hak8or/WeatherSpot/firmware/Network.cpp

#include <SoftwareSerial.h>
#include "Arduino.h"
#include "Heartbeat.h"
#include "Network.h"
#include "Sensors.h"

/**
 * @brief Sends a peice of data over TCP to our backend.
 * @details Does a DNS lookup for our backend, sets up a TCP connection, and sends our data.
 *
 * @param  sensor_data The sensor data struct worth of data we will be sending.
 * @param  series      What series (location) we want our data to be sent to.
 * 
 * @return             True if data was sent succesfully, false if otherwise.
 */
bool Network::send_packet(const Sensors::Sensor_data sensor_data, const String series){
	// Connect to our server.
	if (send_command("AT+CIPSTART=\"TCP\",\"104.131.85.242\",80", "OK", 2, 1500))
		Serial.println(F("Wifi TCP connection created."));
	else{
		Serial.println(F("Wifi TCP connection creation failed."));
		return false;
	}

	// Construct our POST request.
	String post_request = "POST /db/query.php?";
	post_request = post_request + "series=" + series;
	post_request = post_request + "&temperature=" + String(sensor_data.temperature_f);
	post_request = post_request + "&humidity=" + String(sensor_data.humidity);
	post_request = post_request + "&pressure=" + String(sensor_data.pressure);
	post_request = post_request + "&lighting=" + String(sensor_data.light);
	post_request = post_request + "\r\n";

	// Construct the command to begin our POST request.
	String command = "AT+CIPSEND=" + String(post_request.length());

	Serial.print(F("Sending:\n\t"));
	Serial.println(command);
	Serial.print(F("With the contents:\n\t"));
	Serial.println(post_request);

	// Tell the wifi module we want to send a HTTP request.
	if (send_command(command, ">", 1, 1500))
		Serial.println(F("Wifi queried for HTTP contents."));
	else{
		Serial.println(F("Wifi module didn't query what http contents to send, error."));
		return false;
	}

	// And now we send our POST request.
	if (send_command(post_request, "OK", 2, 5000))
		Serial.println(F("Wifi POST request sent succesfully."));
	else{
		Serial.println(F("Wifi POST request failed."));
		return false;
	}

	// It seems that CIPSEND automatically closes the TCP connection or our backend
	// terminates the TCP connection, so CIPCLOSE isn't needed.
	return true;
}

/**
 * @brief Connects to a wireless network using the ESP module.
 * 
 * @param SSID      The SSID of the wireless network we want to connect to.
 * @param password  The password of the wireless network we want to connect to.
 * 
 * @return True if we were able to connect to the network and get an IP, false if otherwise.
 */
bool Network::init_wireless(const String SSID, const String password){
	// Generate the member object
	// Pin D3 -> RX
	// Pin D4 -> TX
	wifi_serial = new SoftwareSerial(4,3);
	wifi_serial->begin(9600);

	// Rest the module so it is in a known state and check if it works.
	if (send_command("AT+RST", "OK", 2, 1500))
		Serial.println(F("Wifi reseting ack recieved."));
	else{
		Serial.println(F("Wifi reseting failed."));
		return false;
	}
	
	// Delay a bit in case we get a "WIFI Disconnect" messege afterwards.
	delay(1500);

	// And the correct wireless mode.
	if (send_command("AT+CWMODE=1", "OK", 2, 1500))
		Serial.println(F("Wifi mode select was succesfull."));
	else{
		Serial.println(F("Wifi mode select failed, no reply or garbage returned."));
		return false;
	}

	// Delay a bit since for some reason the CWMODE seems to return some gunk at the end.
	delay(1500);
	
	// Login to the network.
	// Todo: search for the AP we want to to confirm it exists.
	String command = "AT+CWJAP_CUR=\"" + SSID + "\",\"" + password + "\"";
	if (send_command(command, "WIFI GOT IP", 11, 5000))
		Serial.println("Wifi connected to " + SSID + " network succesfully!");
	else{
		Serial.println("Wifi connected to " + SSID + " network failed.");

		// Damiens WIFI board/network bugs out seemingly always at this point
		// even though he is actually connected, so this is stuck at true. :/
		return true;
	}

	// Allow just a single TCP connection.
	if (send_command("AT+CIPMUX=0", "OK", 2, 1500))
		Serial.println(F("Wifi single TCP setting was succesfull."));
	else{
		Serial.println(F("Wifi single TCP setting failed, no reply or garbage returned."));
		return false;
	}

	// Do a ping request to make sure the server is up.
	if (send_command("AT+PING=\"www.weatherspot.us\"", "OK", 2, 1500))
		Serial.println(F("Wifi ping test to weatherspot.us OK"));
	else{
		Serial.println(F("Wifi ping test to weatherspot.us Failed."));
		return false;
	}

	// Dumps the wifi info to the serial port.
	get_wifi_info();

	return true;
}

/**
 * @brief Dumps wifi network information over to the pc serial.
 */
 void Network::get_wifi_info(void){
	Serial.println(F("============== Wifi Network info vvv"));
	uint32_t start_time = millis();

	// Mirror output of a "get network info" command.
	wifi_serial->println("AT+CIFSR");
	while ((millis() - start_time) < 500)
		if (wifi_serial->available())
			Serial.write(wifi_serial->read());

	Serial.println(F("============== Wifi Network info ^^^"));
}

/**
 * @brief Blocks till either timeout or we find the requested reply on the wifi serial port.
 * 
 * @param reply The reply we are waiting for.
 * @param reply_length Number of chars of our reply.
 * @param milliseconds The timeout for how long we are willing to wait.
 * 
 * @return True if we found the reply within the timeout.
 */
bool Network::find(const String reply, const uint8_t reply_length, const uint16_t milliseconds){
	uint32_t start_time = millis();
	uint8_t  current_reply_index = 0;

	// Make sure we don't spend forever waiting for the char sequence.
	while((millis() - start_time) < milliseconds){
		if (wifi_serial->available() > 0) {
			char reply_char = wifi_serial->read();
			if (reply_char == reply[current_reply_index]){
				// Check if we succesfully compared the entire reply.
				if ((reply_length - 1) == current_reply_index)
					return true;
				else 
					current_reply_index++;
			}
			else{
				// Reset the index back to zero so we can start searching again.
				current_reply_index = 0;

				// Increment buffer index.
				reply_buffer_current_index++;

				// Empty our buffer if it is full.
				if (reply_buffer_current_index == reply_buffer_size){
					reply_buffer_current_index = 0;

					for (int index = 0; index < reply_buffer_size; index++)
						reply_buffer[index] = ' ';
				}

				// Put the char in our buffer.
				reply_buffer[reply_buffer_current_index] = reply_char;
			}
		}
	}

	// If we timed out, then it's considerd we didn't find our char array.
	return false;
}

/**
 * @brief Sends a command to the WIFI module.
 * @details Sends a command to the wifi module, waits for a verification before a timeout.
 * 
 * @param command The command we will be sending.
 * @param reply The reply we expect back.
 * @param reply_length The length of the reply in chars.
 * @param timeout How long we are willing to wait for the reply in milliseconds.
 * 
 * @return True if command and verification within timeout was correct, false if otherwise.
 */
bool Network::send_command(const String command, const String reply, const uint8_t reply_length, const uint16_t timeout){
	// Send the command.
	wifi_serial->println(command);

	// Check if we got the expected reply back.
	if(!find(reply, reply_length, timeout)){
		Serial.print("Command failed: ");
		Serial.println(command);

		// Dump the buffer.
		Serial.println(F("Reply ------- start  vvvv"));
		for (int i = 0; i < reply_buffer_current_index; i++)
			Serial.print(reply_buffer[i]);
		Serial.println(F("Reply ------- end    ^^^^"));

		// Empty our buffer.
		reply_buffer_current_index = 0;
		for (int index = 0; index < reply_buffer_size; index++)
			reply_buffer[index] = ' ';

		return false;
	} else
		return true;
}
