hak8or/WeatherSpot/firmware/Heartbeat.h

#pragma once

/**
 * Controls a heartbeat LED for knowing the state of our system.
 */
class Heartbeat
{
public:
	/**
	* @brief Starts the heartbeat LED on PB5 using a timer.
	*/
	static void start(void);

	/**
	 * @brief Stops the heartbeat LED and timer.
	 */
	static void stop(void);

	/**
	 * @brief ISR for toggling the heartbeat LED.
	 */
	inline static void toggle(void);

	/**
	 * @brief Blinks the LED much quicker to show that we are in an error state.
	 */
	static void panic(void);
};
